Ralim/Z80Cube/Code/MCULoader/MCULoader/main.cpp

/*
 * MCULoader.cpp
 *
 * Created: 10/03/2016 9:09:44 PM
 * Author : Ralim
 */ 

#include <avr/io.h>
#include "AddressBus.h"
AddressBus dataBus;
void setup()
{
	
}
int main(void)
{
	setup();//setup the system
    /* Replace with your application code */
    while (1) 
    {
    }
}
